Genei180/ZINC/ZINC_Files/Depreciated/1.1/STEP/STANDARD/TRIGGER_STANDARD[1.1].step

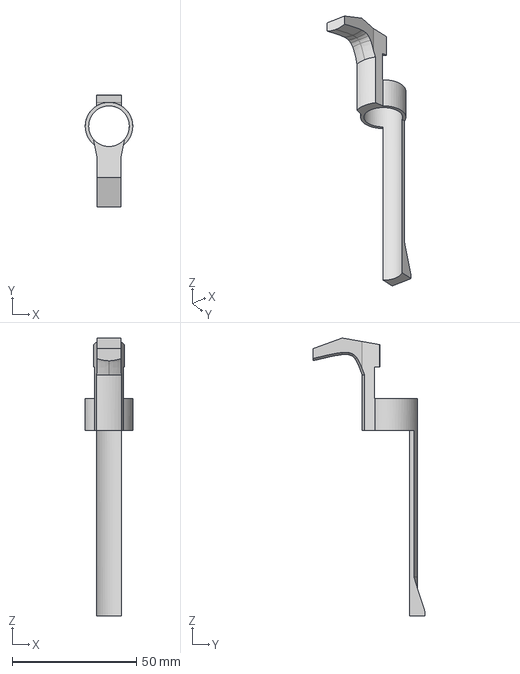
[picture p14: CAD file, 2024-03-12]
ZINC_Files/Depreciated/1.1/STEP/STANDARD/TRIGGER_STANDARD[1.1].step
19.1 x 45.2 x 111.7 mm
