Genei180/ZINC/ZINC_Files/Depreciated/1.1/STL/MAGAZINE/MAG_BODY_11_UNDERSIZE[1.1].stl

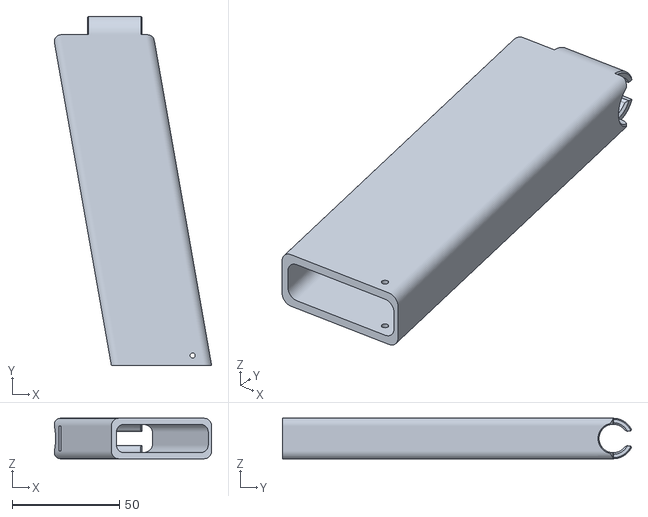
[picture p15: CAD file, 2024-03-12]
ZINC_Files/Depreciated/1.1/STL/MAGAZINE/MAG_BODY_11_UNDERSIZE[1.1].stl
73.3 x 162.5 x 18.9
