Genei180/ZINC/ZINC_Files/Depreciated/1.1/STL/OVERSIZE/CATCH_OVERSIZE[1.1].stl

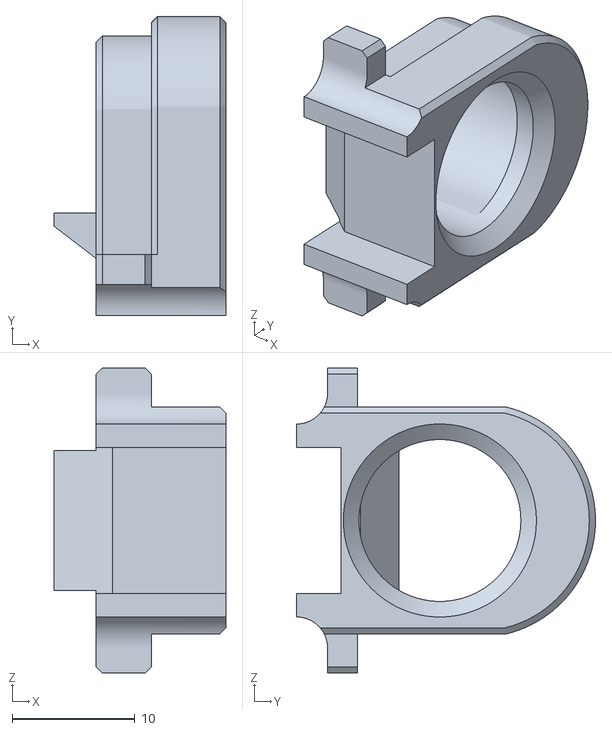
[picture p16: CAD file, 2024-03-12]
ZINC_Files/Depreciated/1.1/STL/OVERSIZE/CATCH_OVERSIZE[1.1].stl
14.0 x 24.4 x 24.9
