Genei180/ZINC/ZINC_Files/Depreciated/1.1/STL/PULL[1.1].stl

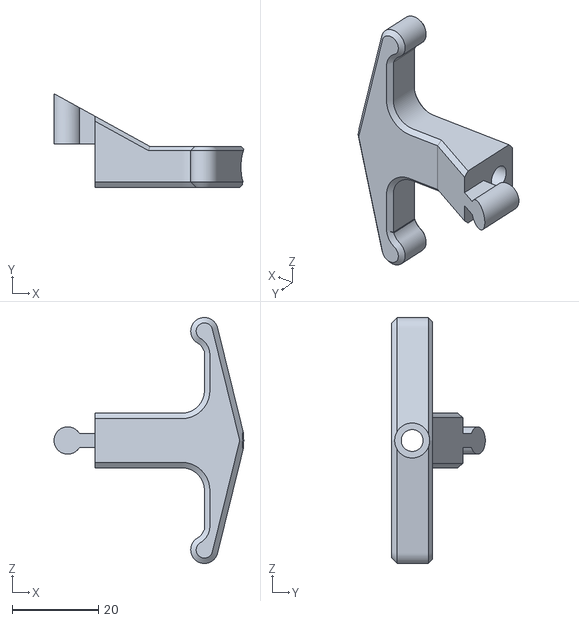
[picture p17: CAD file, 2024-03-12]
ZINC_Files/Depreciated/1.1/STL/PULL[1.1].stl
44.1 x 21.8 x 57.1
