Genei180/ZINC/ZINC_Files/Depreciated/1.1/STL/STANDARD/FRAME_TOP_RAIL_INCLUDED_STANDARD[1.1].stl

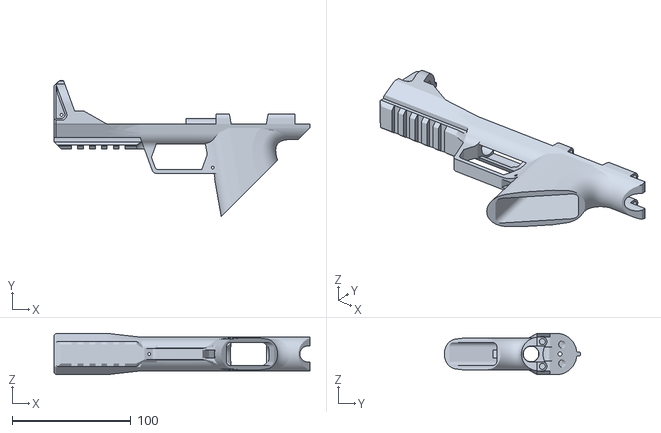
[picture p18: CAD file, 2024-03-12]
ZINC_Files/Depreciated/1.1/STL/STANDARD/FRAME_TOP_RAIL_INCLUDED_STANDARD[1.1].stl
215.9 x 115.0 x 34.9
