Genei180/ZINC/ZINC_Files/Depreciated/1.2/STL/FRAME_BOTTOM[1.2].stl

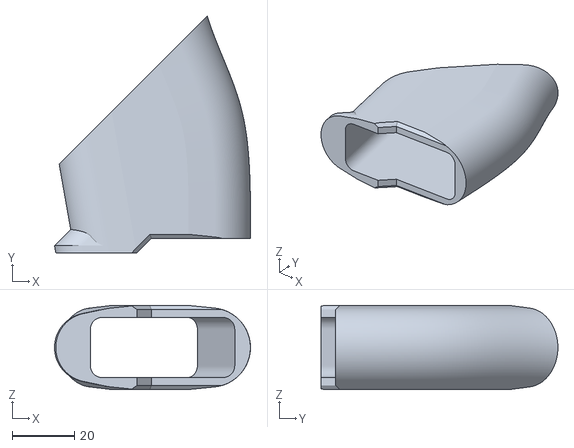
[picture p19: CAD file, 2024-03-12]
ZINC_Files/Depreciated/1.2/STL/FRAME_BOTTOM[1.2].stl
62.9 x 76.0 x 27.0
