Genei180/ZINC/ZINC_Files/Depreciated/1.2/STL/MAGAZINE/MAG_BOTTOM_UNDERSIZE[1.1].stl

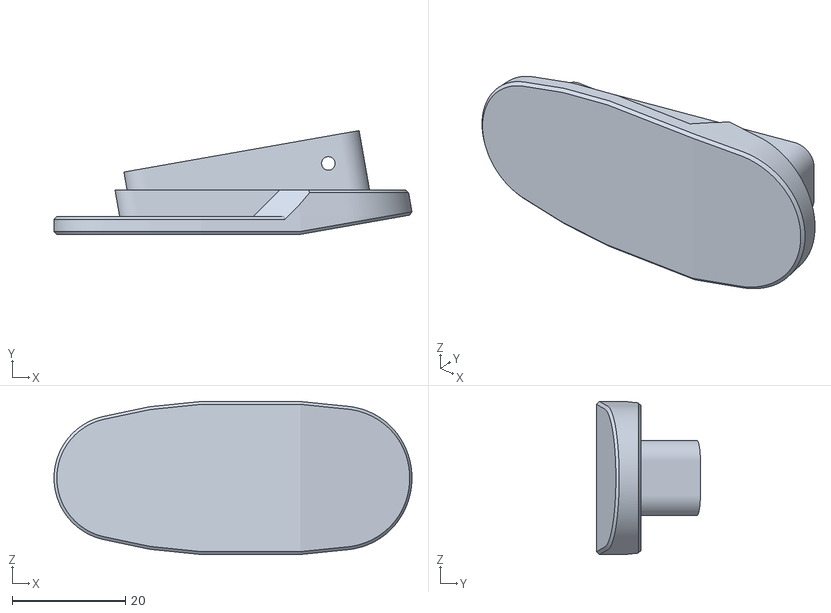
[picture p20: CAD file, 2024-03-12]
ZINC_Files/Depreciated/1.2/STL/MAGAZINE/MAG_BOTTOM_UNDERSIZE[1.1].stl
63.1 x 18.3 x 27.0
