Genei180/ZINC/ZINC_Files/Depreciated/1.2/STL/UNDERSIZE/FRAME_TOP_COMPACT_UNDERSIZE[1.2].stl

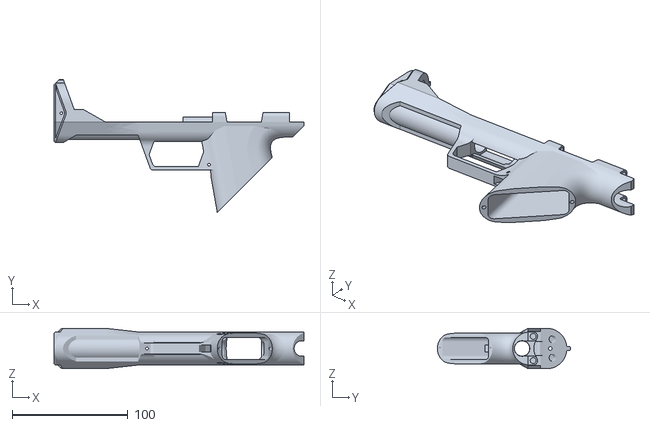
[picture p21: CAD file, 2024-03-12]
ZINC_Files/Depreciated/1.2/STL/UNDERSIZE/FRAME_TOP_COMPACT_UNDERSIZE[1.2].stl
215.9 x 115.0 x 34.9
