Genei180/ZINC/ZINC_Files/Current/STEP/PLUNGER_LOW_POWER_METRIC[2.0].step

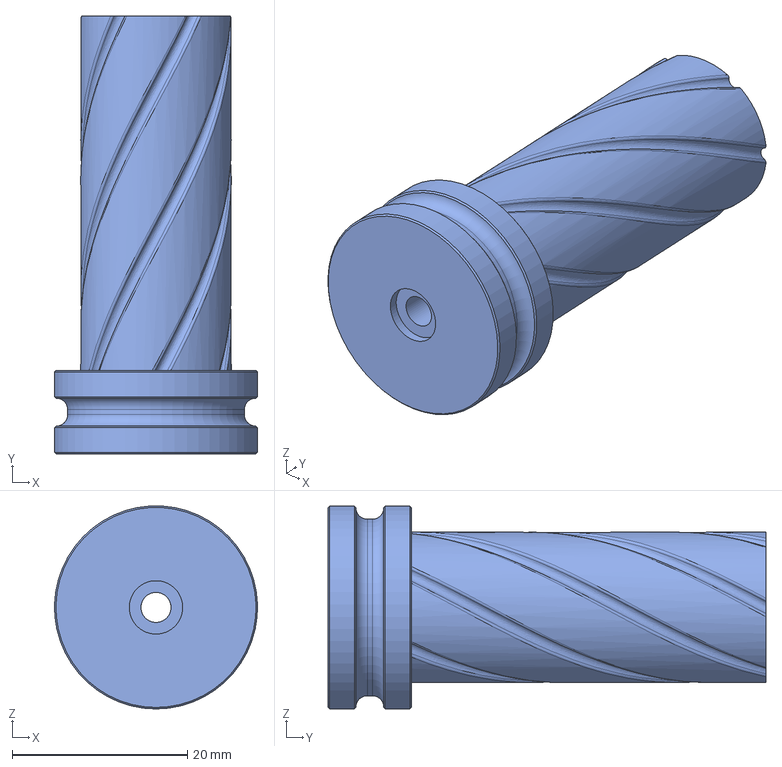
[picture p22: CAD file, 2024-03-26]
ZINC_Files/Current/STEP/PLUNGER_LOW_POWER_METRIC[2.0].step
23.2 x 50.0 x 23.2 mm
