Genei180/ZINC/ZINC_Files/Current/STL/SEAR[2.0].stl

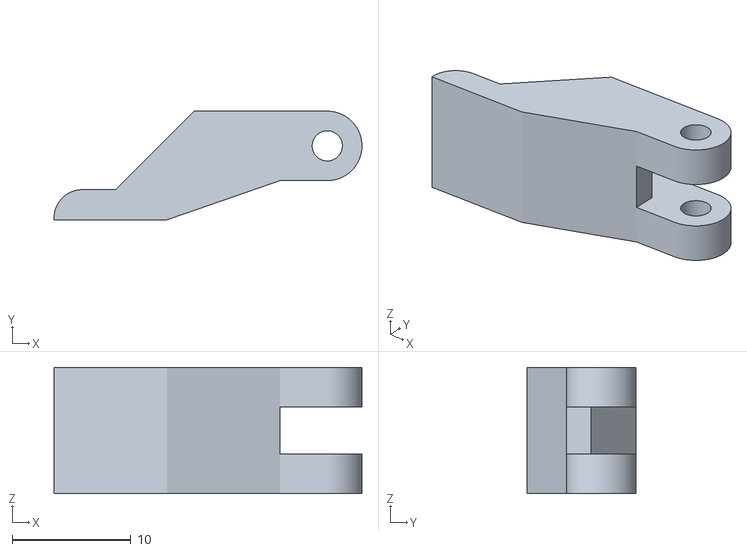
[picture p23: CAD file, 2024-03-12]
ZINC_Files/Current/STL/SEAR[2.0].stl
25.9 x 9.14 x 10.6
