Genei180/ZINC/ZINC_Files/Depreciated/1.0/STEP/SLIDE_FRONT.step

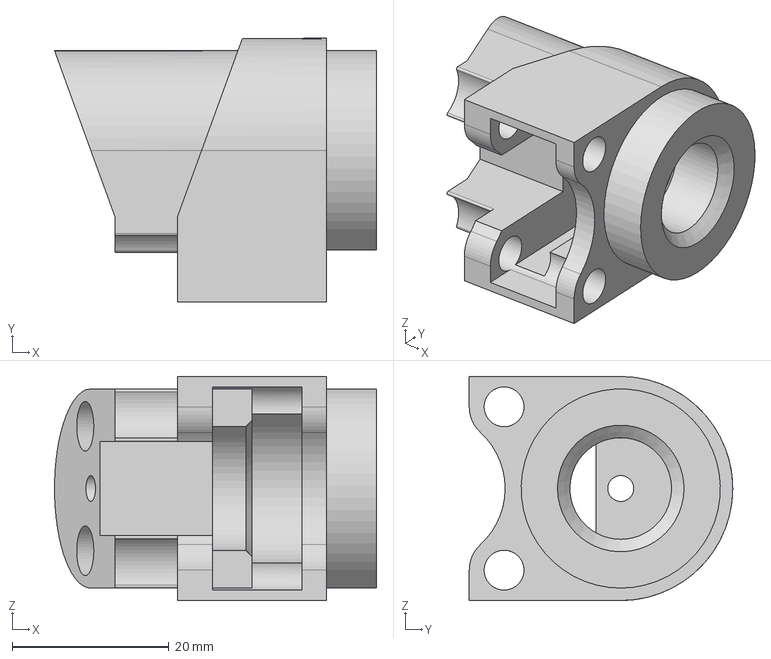
[picture p24: CAD file, 2024-03-12]
ZINC_Files/Depreciated/1.0/STEP/SLIDE_FRONT.step
41.1 x 33.6 x 28.6 mm
