Genei180/ZINC/ZINC_Files/Depreciated/1.0/STL/Depreciated/FRAME_RAIL_ONE_PIECE.stl

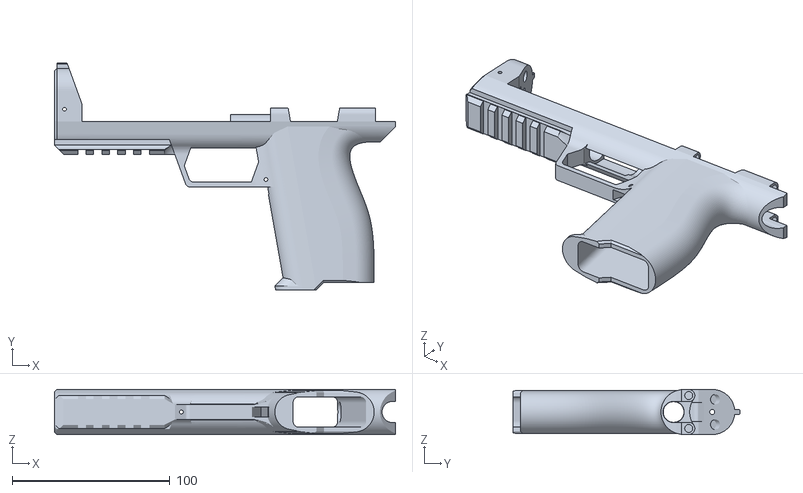
[picture p25: CAD file, 2024-03-12]
ZINC_Files/Depreciated/1.0/STL/Depreciated/FRAME_RAIL_ONE_PIECE.stl
215.9 x 143.5 x 28.6
