Genei180/ZINC/ZINC_Files/Depreciated/1.0/STL/TRIGGER_RIGHT.stl

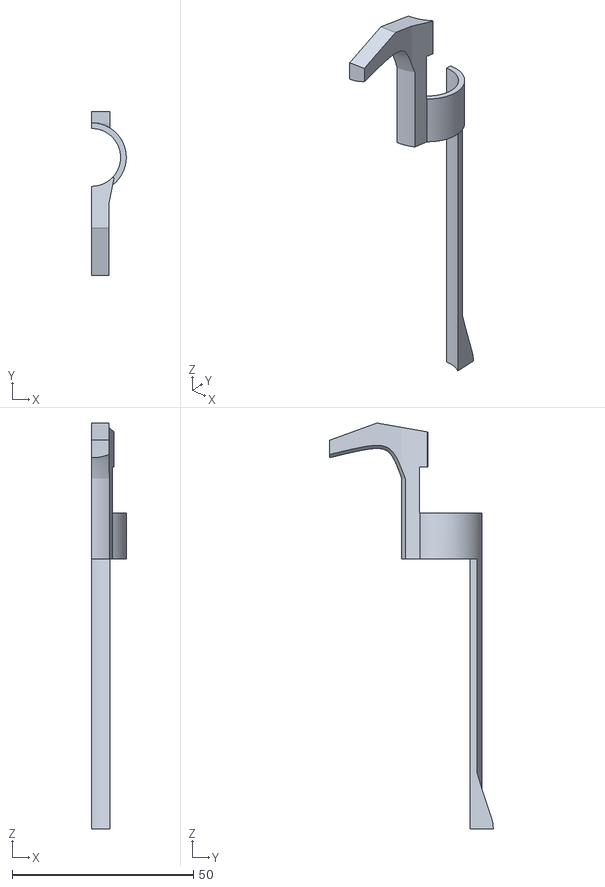
[picture p26: CAD file, 2024-03-12]
ZINC_Files/Depreciated/1.0/STL/TRIGGER_RIGHT.stl
9.56 x 45.2 x 112.1
