Genei180/ZINC/ZINC_Files/Depreciated/1.1/STEP/MAGAZINE/MAG_BODY_9_UNDERSIZE[1.1].step

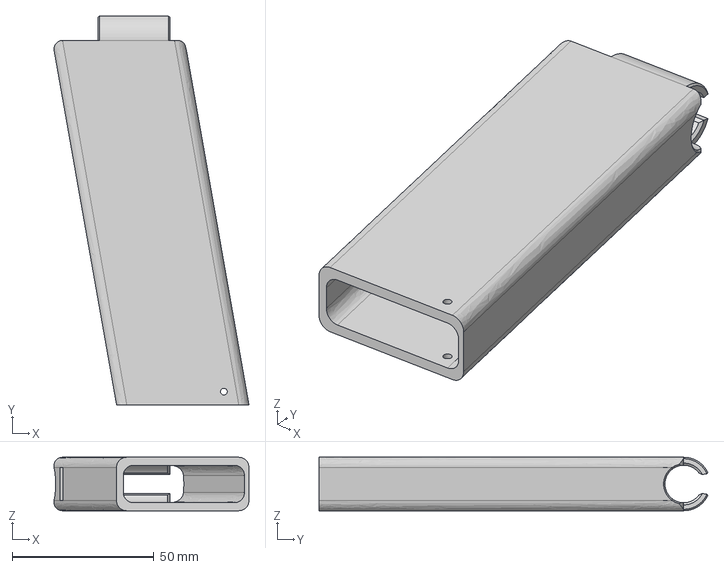
[picture p27: CAD file, 2024-03-12]
ZINC_Files/Depreciated/1.1/STEP/MAGAZINE/MAG_BODY_9_UNDERSIZE[1.1].step
68.8 x 137.1 x 18.9 mm
