Genei180/ZINC/ZINC_Files/Depreciated/1.1/STEP/STANDARD/FRAME_TOP_RAIL_STANDARD[1.1].step

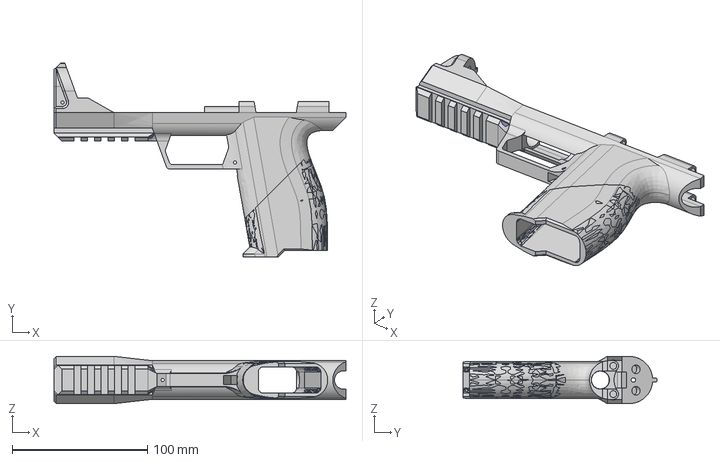
[picture p28: CAD file, 2024-03-12]
ZINC_Files/Depreciated/1.1/STEP/STANDARD/FRAME_TOP_RAIL_STANDARD[1.1].step
215.9 x 143.5 x 34.9 mm
FRAME_BOTTOM[1.1]
