Genei180/ZINC/ZINC_Files/Depreciated/1.1/STL/MAGAZINE/MAG_RELEASE[1.1].stl

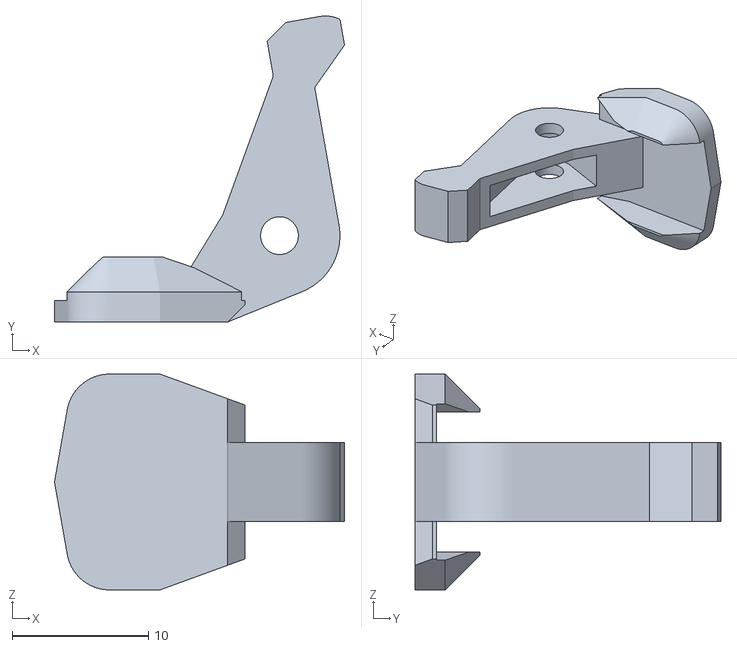
[picture p29: CAD file, 2024-03-12]
ZINC_Files/Depreciated/1.1/STL/MAGAZINE/MAG_RELEASE[1.1].stl
21.3 x 22.5 x 15.9
