Genei180/ZINC/ZINC_Files/Depreciated/1.1/STL/TOLERANCE_GAUGE[1.1].stl

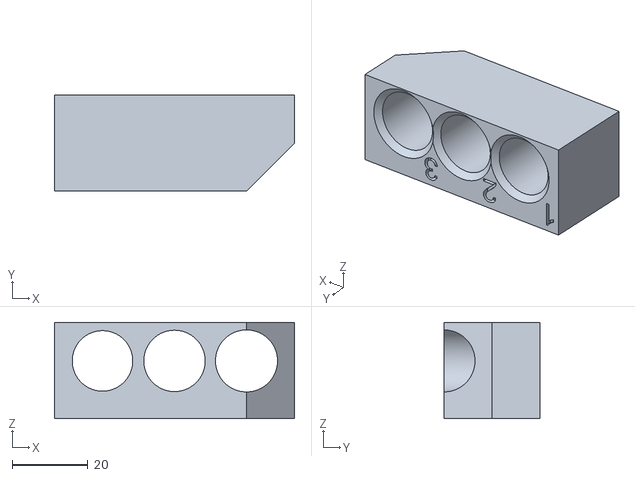
[picture p30: CAD file, 2024-03-12]
ZINC_Files/Depreciated/1.1/STL/TOLERANCE_GAUGE[1.1].stl
63.5 x 25.4 x 25.4
