Genei180/ZINC/ZINC_Files/Depreciated/1.2/STL/MUZZLE_COMPACT[1.2].stl

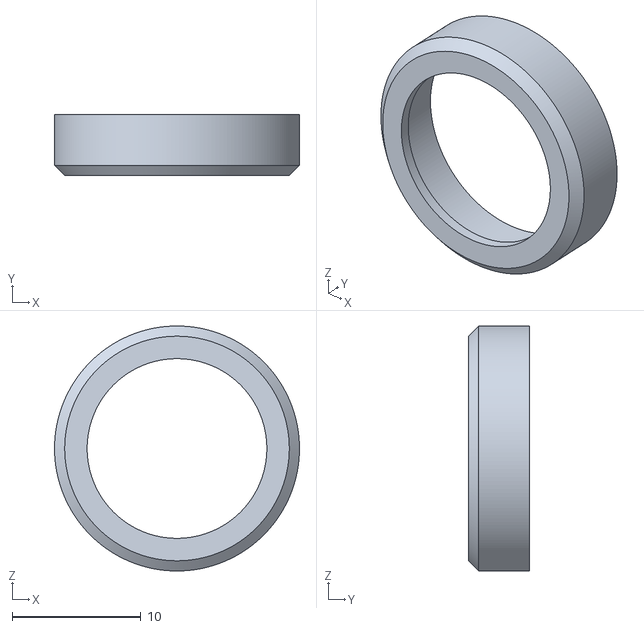
[picture p31: CAD file, 2024-03-12]
ZINC_Files/Depreciated/1.2/STL/MUZZLE_COMPACT[1.2].stl
19.0 x 4.76 x 19.0
