Genei180/ZINC/ZINC_Files/Current/STEP/REAR_METRIC[2.0].step

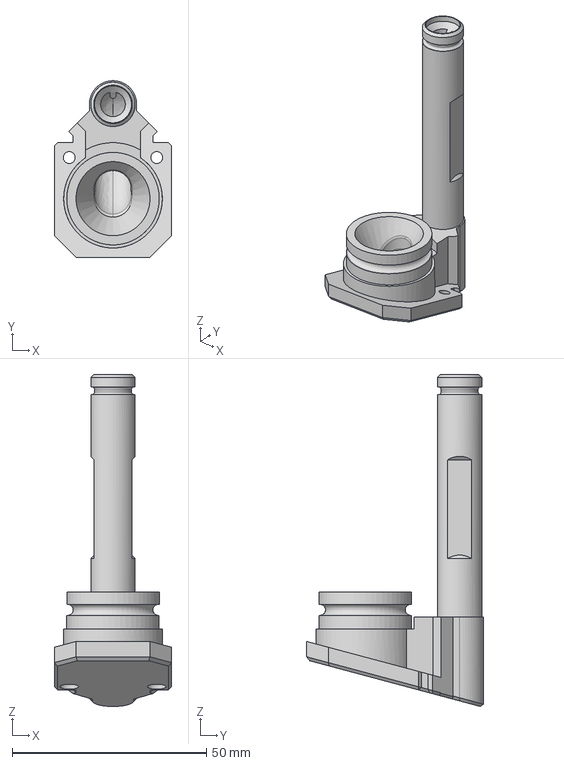
[picture p32: CAD file, 2024-03-14]
ZINC_Files/Current/STEP/REAR_METRIC[2.0].step
30.2 x 45.5 x 85.4 mm
