Genei180/ZINC/ZINC_Files/Depreciated/1.0/STEP/SLIDE_REAR.step

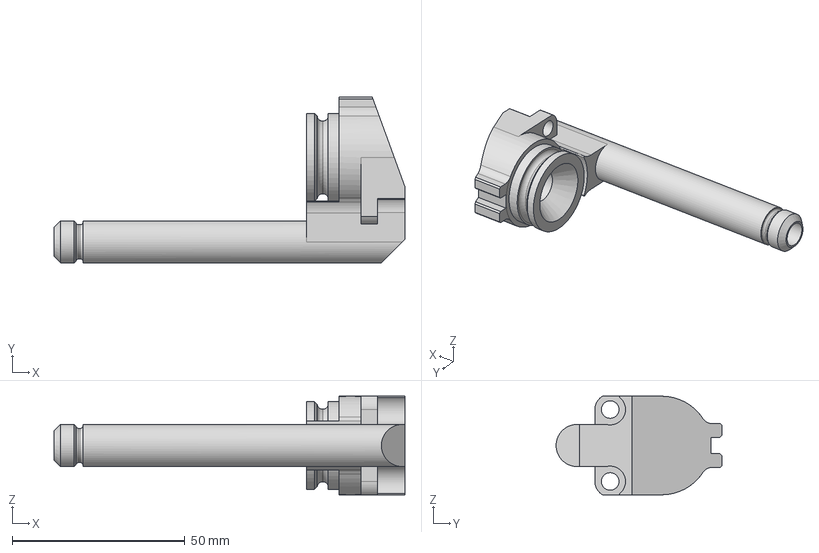
[picture p33: CAD file, 2024-03-12]
ZINC_Files/Depreciated/1.0/STEP/SLIDE_REAR.step
101.6 x 48.0 x 28.6 mm
