Genei180/ZINC/ZINC_Files/Depreciated/1.0/STL/Depreciated/FRAME_TOP_RAIL_INCLUDED.stl

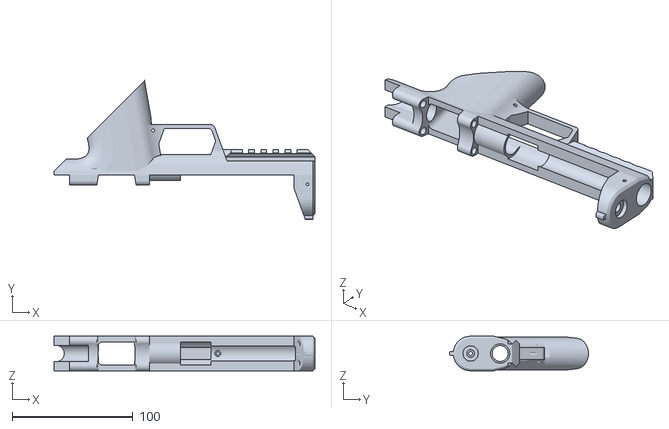
[picture p34: CAD file, 2024-03-12]
ZINC_Files/Depreciated/1.0/STL/Depreciated/FRAME_TOP_RAIL_INCLUDED.stl
215.9 x 115.0 x 28.6
