Genei180/ZINC/ZINC_Files/Depreciated/1.1/STEP/STANDARD/CATCH_STANDARD[1.1].step

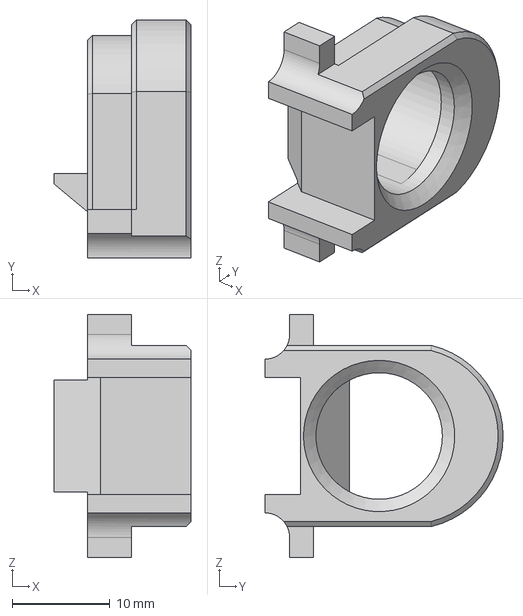
[picture p35: CAD file, 2024-03-12]
ZINC_Files/Depreciated/1.1/STEP/STANDARD/CATCH_STANDARD[1.1].step
14.0 x 24.4 x 24.9 mm
