Genei180/ZINC/ZINC_Files/Depreciated/1.2/STL/STANDARD/TRIGGER_LEFT_STANDARD[1.2].stl

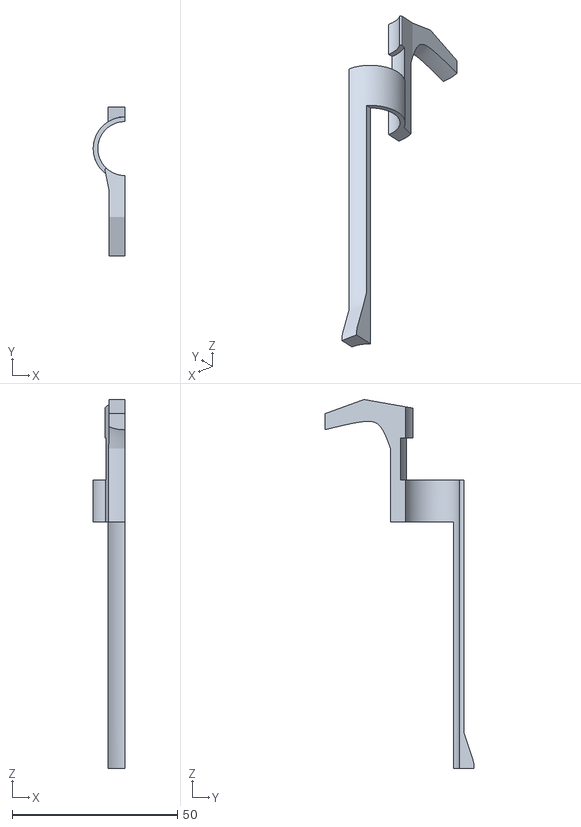
[picture p36: CAD file, 2024-03-12]
ZINC_Files/Depreciated/1.2/STL/STANDARD/TRIGGER_LEFT_STANDARD[1.2].stl
9.56 x 45.2 x 111.7
