Genei180/ZINC/ZINC_Files/Current/STEP/PLUNGER_CORE.step

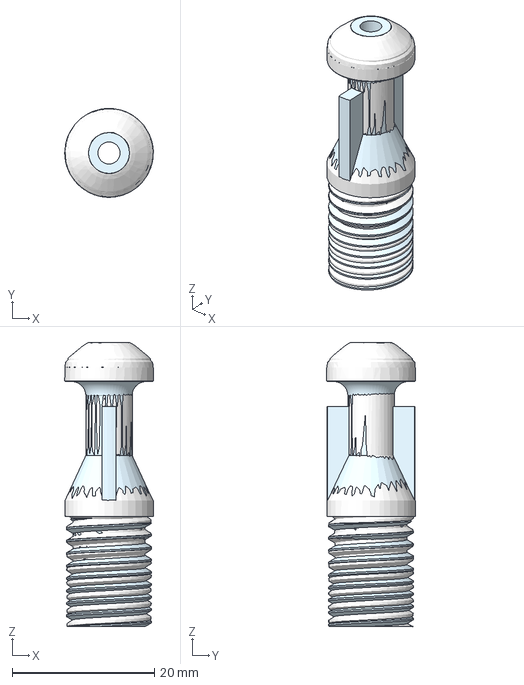
[picture p37: CAD file, 2024-03-14]
ZINC_Files/Current/STEP/PLUNGER_CORE.step
12.5 x 12.5 x 40.0 mm
