Genei180/ZINC/ZINC_Files/Depreciated/1.0/STEP/FRAME_TOP_RAIL_ONE_PIECE.step

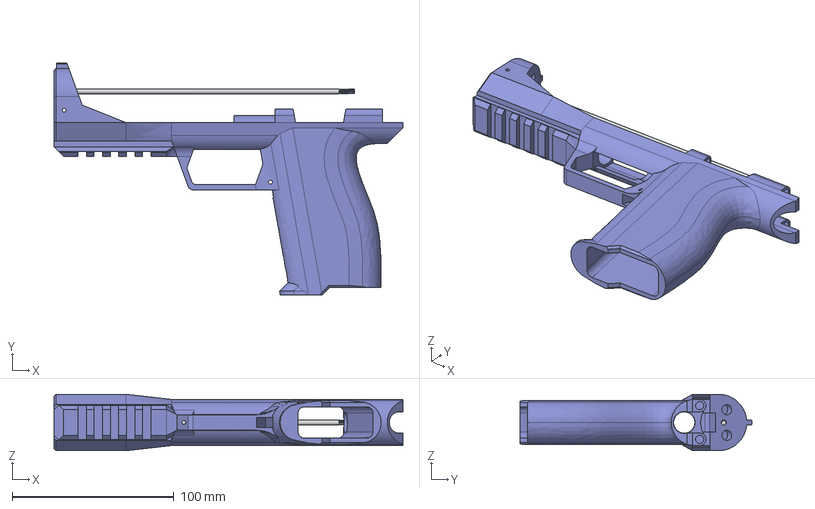
[picture p38: CAD file, 2024-03-12]
ZINC_Files/Depreciated/1.0/STEP/FRAME_TOP_RAIL_ONE_PIECE.step
215.9 x 143.5 x 34.9 mm
1/8 OD Connecting rod
