Genei180/ZINC/ZINC_Files/Depreciated/1.0/STL/Depreciated/FRAME_COMPACT_ONE_PIECE.stl

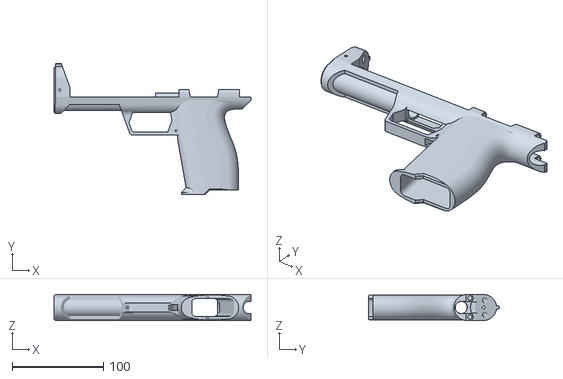
[picture p39: CAD file, 2024-03-12]
ZINC_Files/Depreciated/1.0/STL/Depreciated/FRAME_COMPACT_ONE_PIECE.stl
215.9 x 143.5 x 28.6
