Genei180/ZINC/ZINC_Files/Depreciated/1.0/STL/Magazine/MAG_BODY_COMPACT.stl

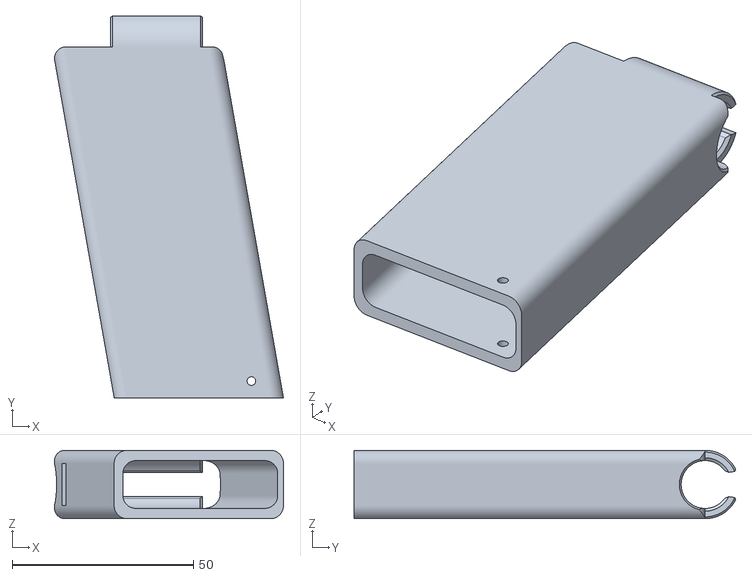
[picture p40: CAD file, 2024-03-12]
ZINC_Files/Depreciated/1.0/STL/Magazine/MAG_BODY_COMPACT.stl
63.2 x 105.4 x 18.9
