Genei180/ZINC/ZINC_Files/Depreciated/1.1/STL/OVERSIZE/FRAME_TOP_RAIL_OVERSIZE[1.1].stl

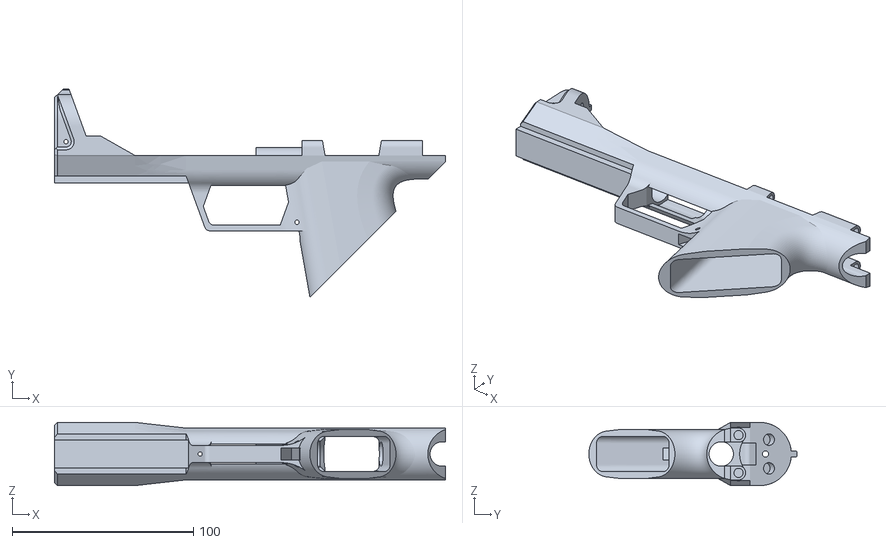
[picture p41: CAD file, 2024-03-12]
ZINC_Files/Depreciated/1.1/STL/OVERSIZE/FRAME_TOP_RAIL_OVERSIZE[1.1].stl
215.9 x 115.0 x 34.9
