Genei180/ZINC/ZINC_Files/Depreciated/1.1/STL/SLIDE_REAR_PULL[1.1].stl

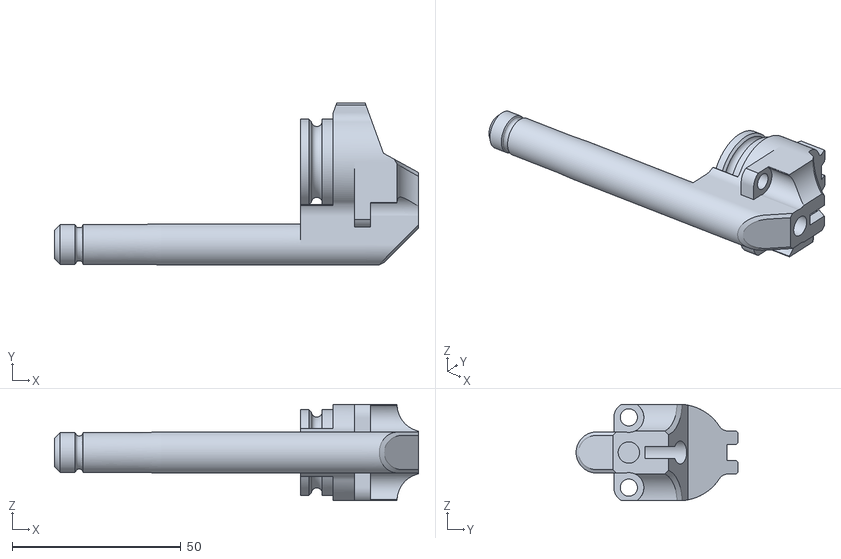
[picture p42: CAD file, 2024-03-12]
ZINC_Files/Depreciated/1.1/STL/SLIDE_REAR_PULL[1.1].stl
107.9 x 48.0 x 28.6
