Genei180/ZINC/ZINC_Files/Depreciated/1.2/STL/MAGAZINE/MAG_BODY_7_UNDERSIZE[1.1].stl

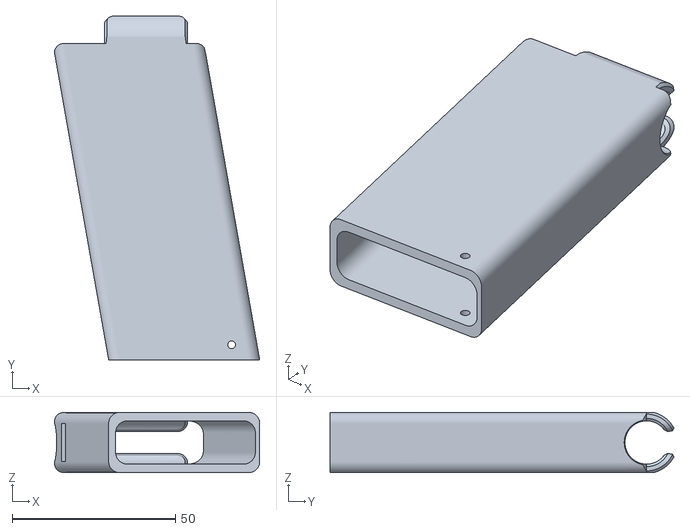
[picture p43: CAD file, 2024-03-12]
ZINC_Files/Depreciated/1.2/STL/MAGAZINE/MAG_BODY_7_UNDERSIZE[1.1].stl
62.9 x 105.3 x 18.4
