Genei180/ZINC/ZINC_Files/Current/STEP/GUARD_RIGHT[2.0].step

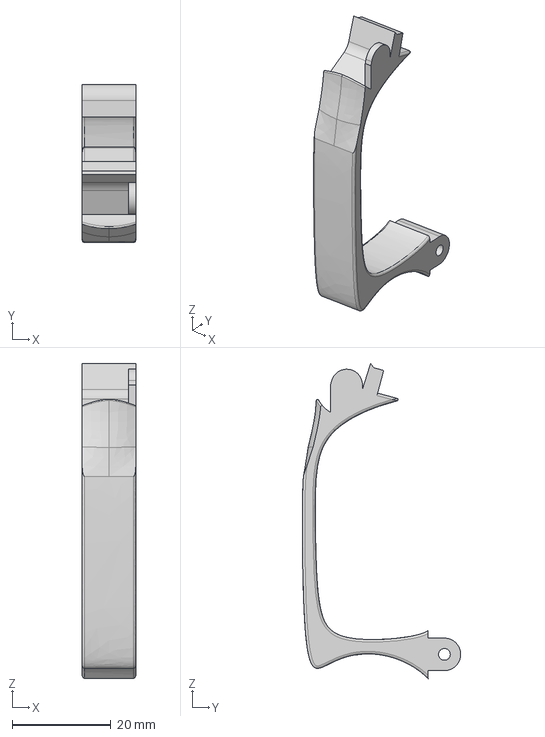
[picture p44: CAD file, 2024-03-12]
ZINC_Files/Current/STEP/GUARD_RIGHT[2.0].step
10.9 x 32.1 x 63.8 mm
