Genei180/ZINC/ZINC_Files/Depreciated/1.1/STEP/MAGAZINE/MAG_BODY_13_UNDERSIZE[1.1].step

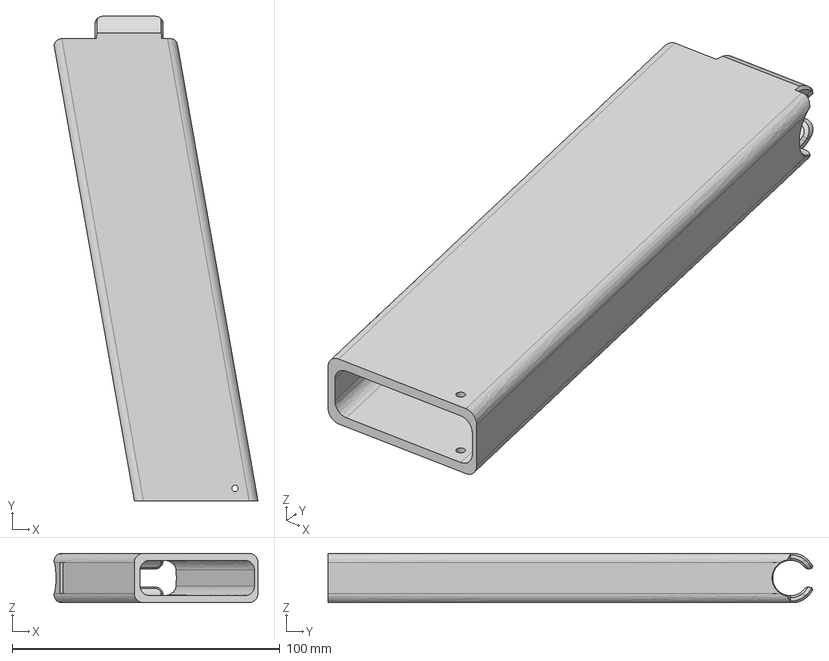
[picture p45: CAD file, 2024-03-12]
ZINC_Files/Depreciated/1.1/STEP/MAGAZINE/MAG_BODY_13_UNDERSIZE[1.1].step
76.3 x 181.2 x 18.4 mm
