Genei180/ZINC/ZINC_Files/Current/STEP/BASE[2.0].step

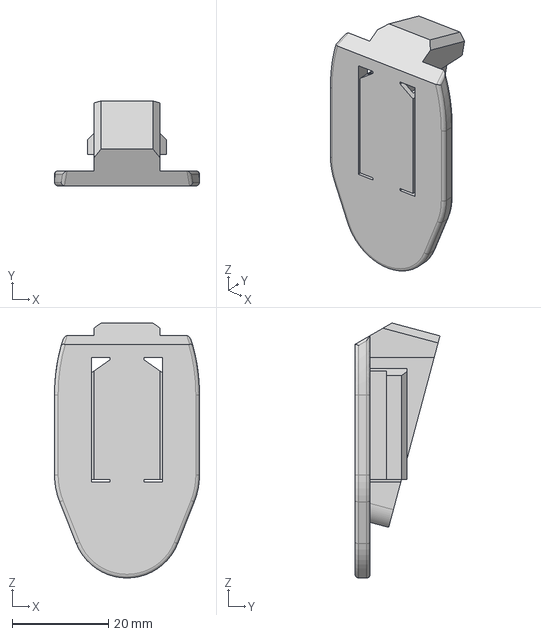
[picture p46: CAD file, 2024-03-12]
ZINC_Files/Current/STEP/BASE[2.0].step
30.2 x 17.7 x 53.1 mm
