Genei180/ZINC/ZINC_Files/Depreciated/1.0/STL/Depreciated/FRAME_FRONT_COMPACT.stl

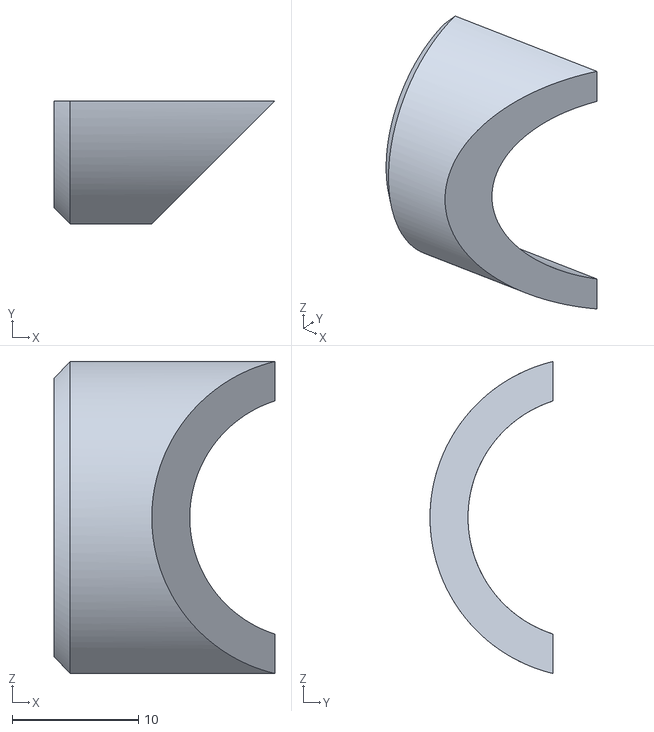
[picture p47: CAD file, 2024-03-12]
ZINC_Files/Depreciated/1.0/STL/Depreciated/FRAME_FRONT_COMPACT.stl
17.5 x 9.74 x 24.7
