Genei180/ZINC/ZINC_Files/Current/STEP/TRIGGER[2.0].step

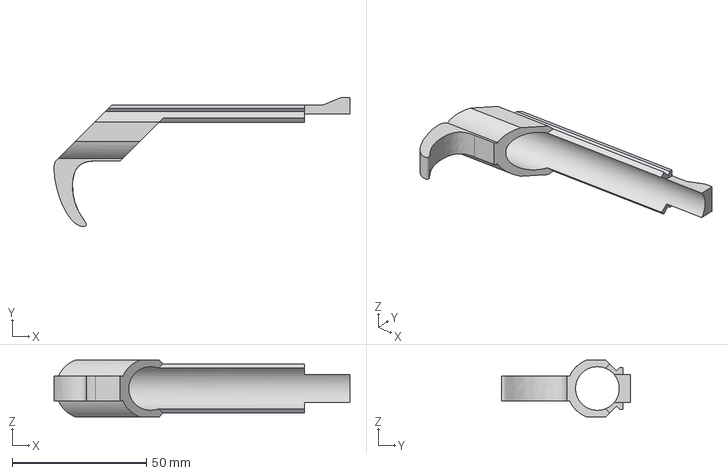
[picture p48: CAD file, 2024-03-12]
ZINC_Files/Current/STEP/TRIGGER[2.0].step
110.2 x 48.1 x 21.1 mm
