Genei180/ZINC/ZINC_Files/Current/STEP/RELEASE_RIGHT[2.0].step

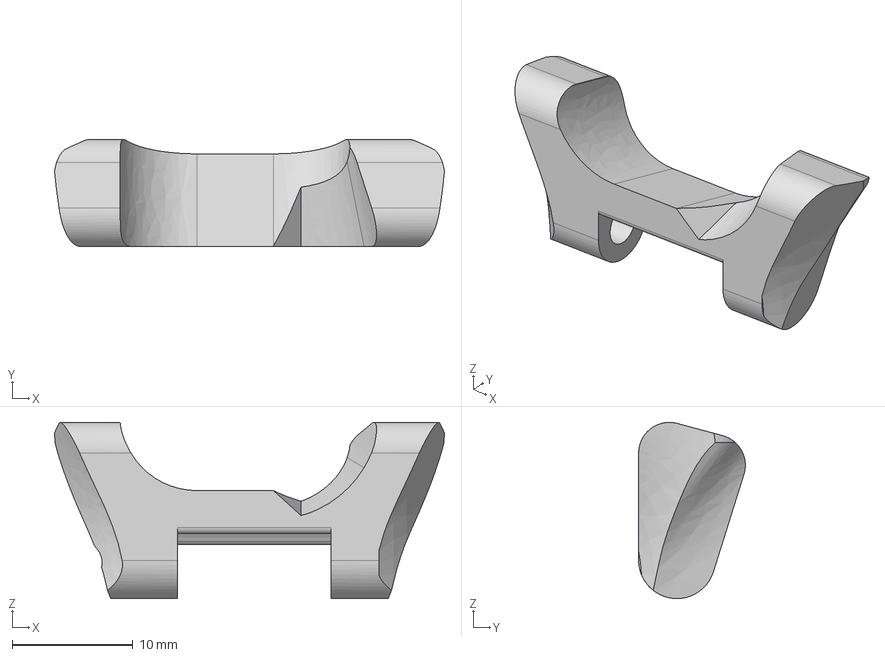
[picture p49: CAD file, 2024-03-12]
ZINC_Files/Current/STEP/RELEASE_RIGHT[2.0].step
32.3 x 8.85 x 14.6 mm
