Genei180/ZINC/ZINC_Files/Depreciated/1.0/STL/SEAR.stl

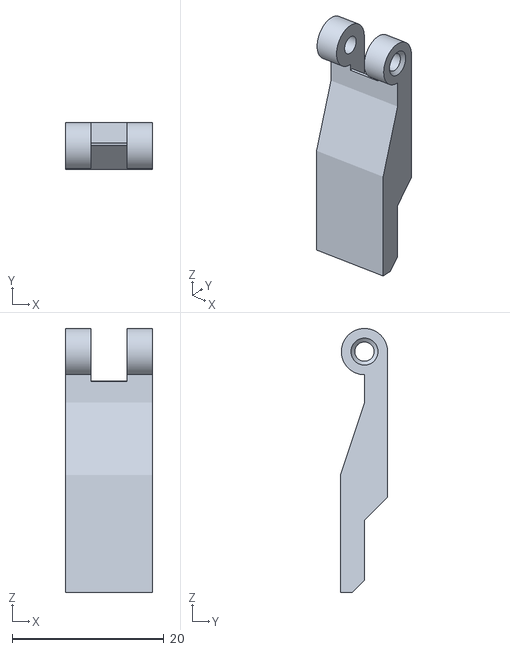
[picture p50: CAD file, 2024-03-12]
ZINC_Files/Depreciated/1.0/STL/SEAR.stl
11.4 x 6.22 x 34.8
