Genei180/ZINC/ZINC_Files/Current/STEP/SLIDE[2.0].step

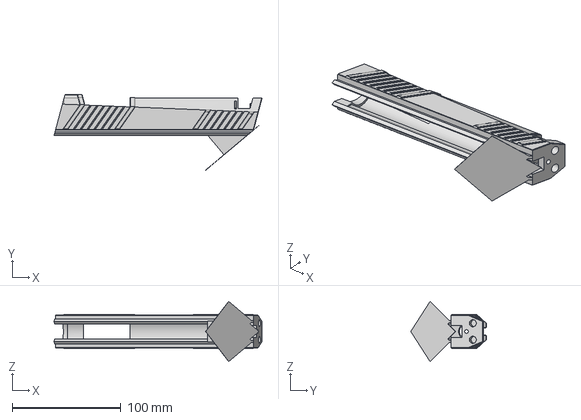
[picture p51: CAD file, 2024-03-12]
ZINC_Files/Current/STEP/SLIDE[2.0].step
191.7 x 69.7 x 55.4 mm
