Genei180/ZINC/ZINC_Files/Current/STEP/CATCH[2.0].step

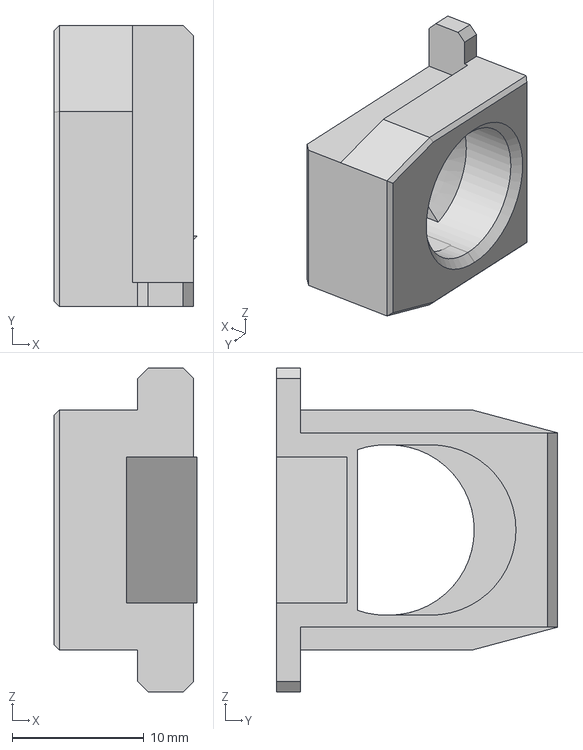
[picture p52: CAD file, 2024-03-12]
ZINC_Files/Current/STEP/CATCH[2.0].step
10.9 x 21.4 x 24.6 mm
