Genei180/ZINC/ZINC_Files/Current/STEP/COVER[2.0].step

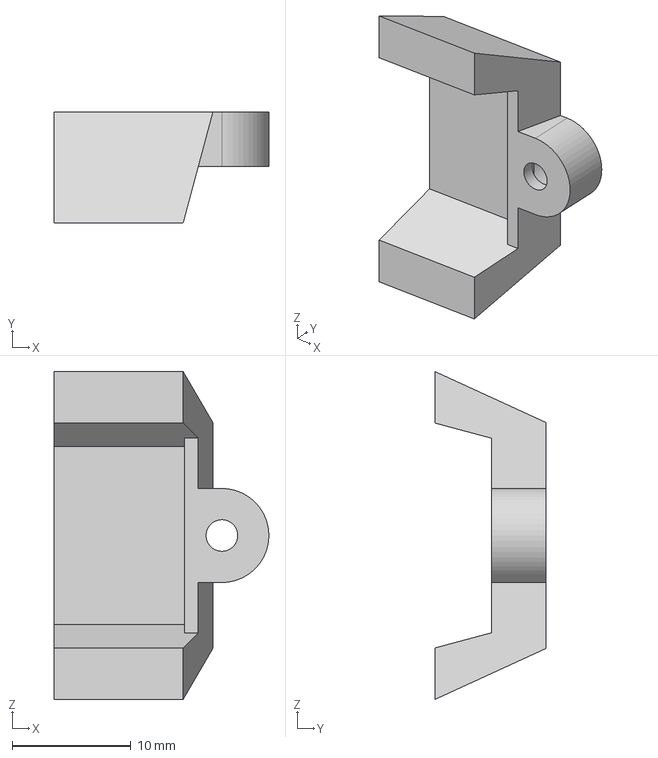
[picture p53: CAD file, 2024-03-12]
ZINC_Files/Current/STEP/COVER[2.0].step
18.1 x 9.40 x 27.7 mm
