Genei180/ZINC/ZINC_Files/Current/STEP/PLUNGER_HIGH_POWER[2.0].step

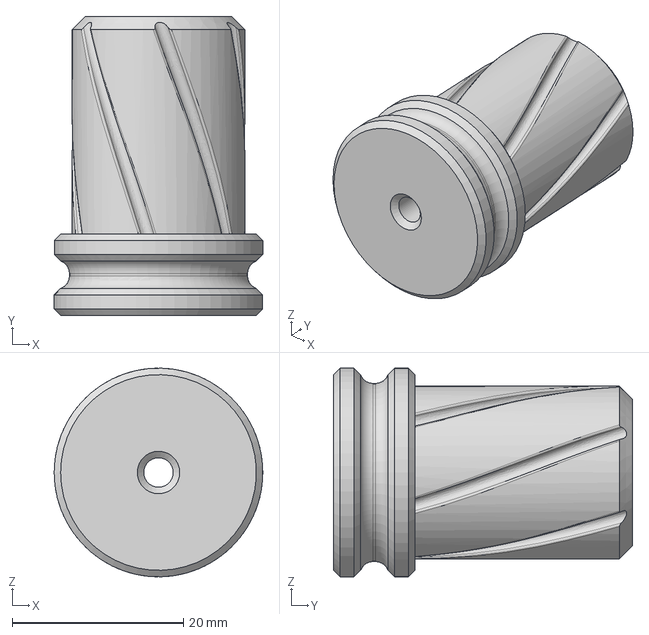
[picture p54: CAD file, 2024-03-12]
ZINC_Files/Current/STEP/PLUNGER_HIGH_POWER[2.0].step
24.4 x 34.9 x 24.4 mm
