Genei180/ZINC/ZINC_Files/Current/STEP/MAGAZINE[2.0].step

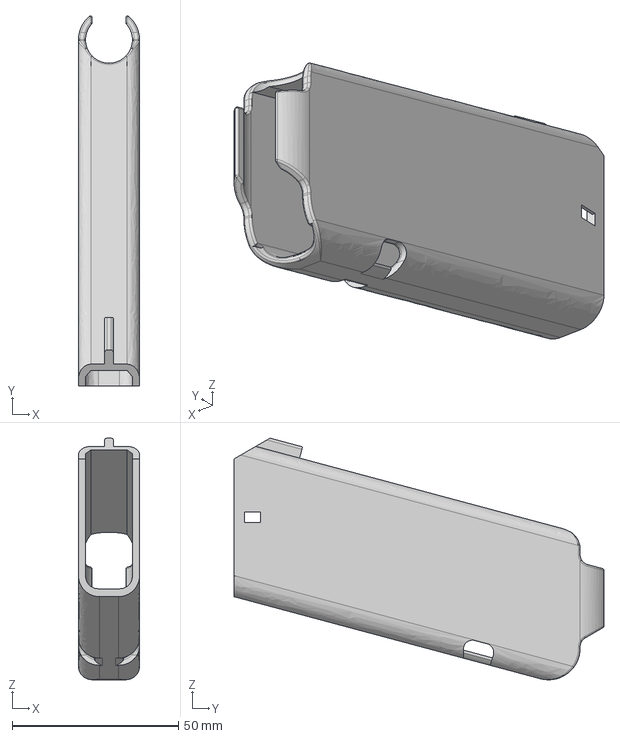
[picture p55: CAD file, 2024-03-12]
ZINC_Files/Current/STEP/MAGAZINE[2.0].step
18.4 x 111.3 x 72.7 mm
