Genei180/ZINC/ZINC_Files/Current/STEP/MAGAZINE_10[2.0].step

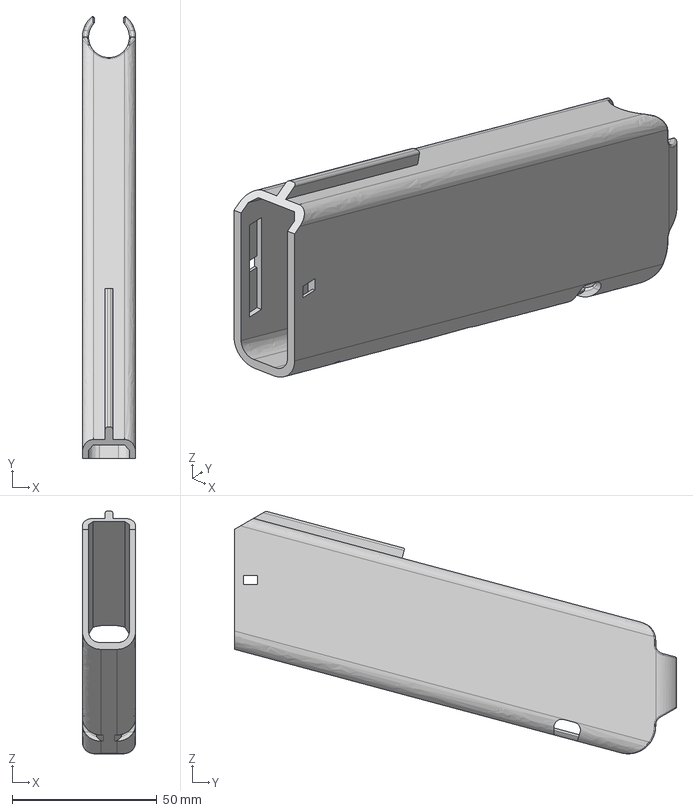
[picture p56: CAD file, 2024-03-12]
ZINC_Files/Current/STEP/MAGAZINE_10[2.0].step
18.4 x 152.5 x 83.7 mm
