Genei180/ZINC/ZINC_Files/Current/STEP/FRAME[2.0].step

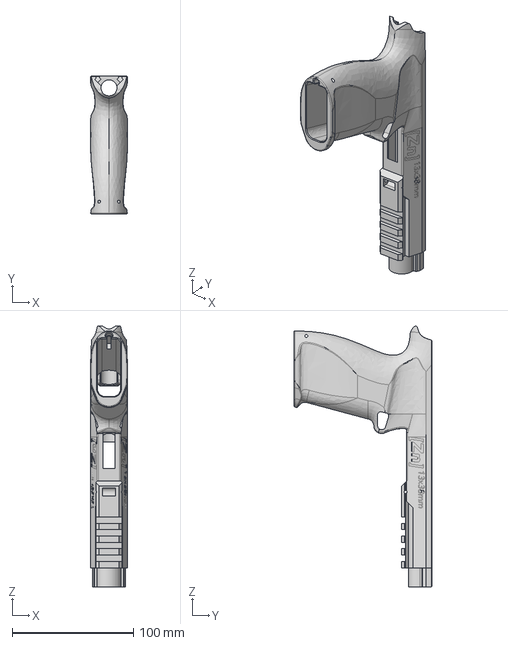
[picture p57: CAD file, 2024-03-12]
ZINC_Files/Current/STEP/FRAME[2.0].step
30.2 x 113.8 x 215.4 mm
