Genei180/ZINC/ZINC_Files/Current/STEP/PLUNGER_LOW_POWER[2.0].step

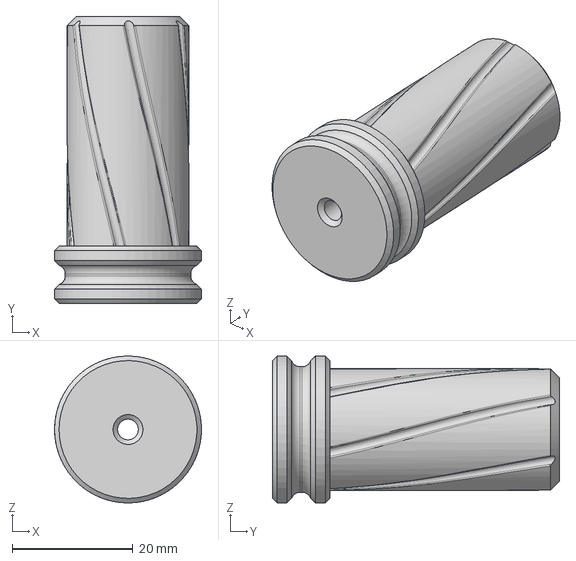
[picture p58: CAD file, 2024-03-12]
ZINC_Files/Current/STEP/PLUNGER_LOW_POWER[2.0].step
24.4 x 47.6 x 24.4 mm
