Genei180/ZINC/ZINC_Files/Current/STEP/FOLLOWER[2.0].step

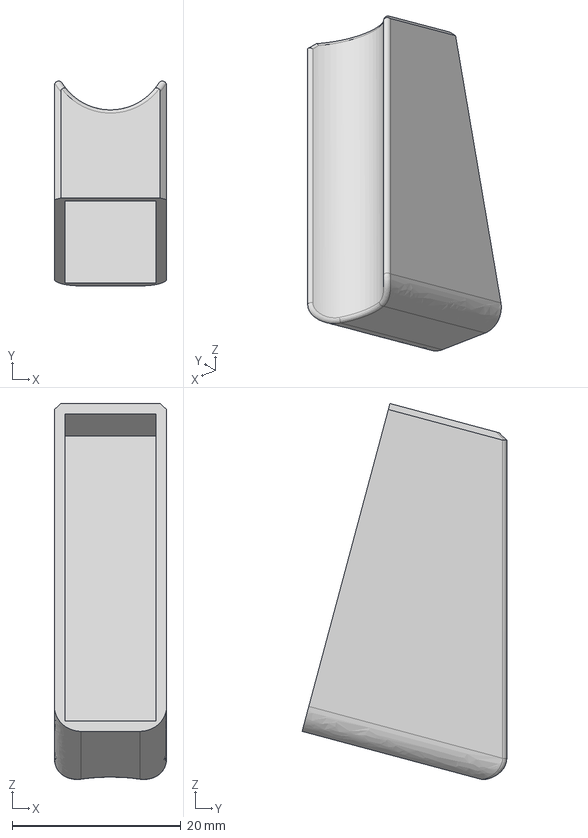
[picture p59: CAD file, 2024-03-12]
ZINC_Files/Current/STEP/FOLLOWER[2.0].step
13.3 x 24.3 x 44.6 mm
