Genei180/ZINC/ZINC_Files/Current/STEP/MAGAZINE_13[2.0].step

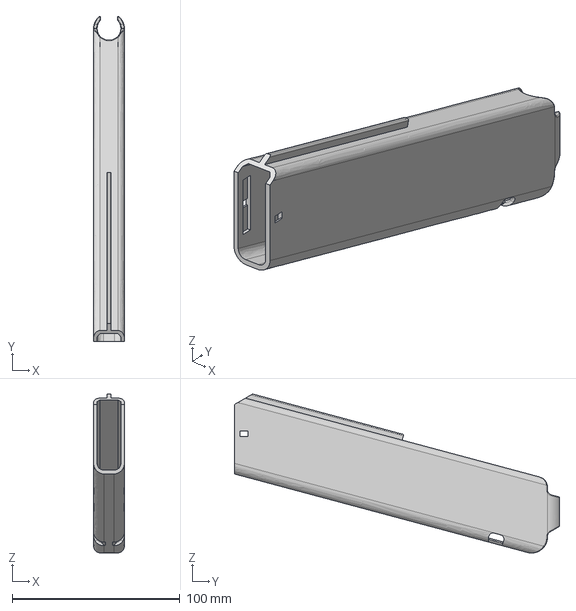
[picture p60: CAD file, 2024-03-12]
ZINC_Files/Current/STEP/MAGAZINE_13[2.0].step
18.4 x 193.8 x 94.8 mm
